Fascial/Stick-For-Blind/photos/image2.jpg

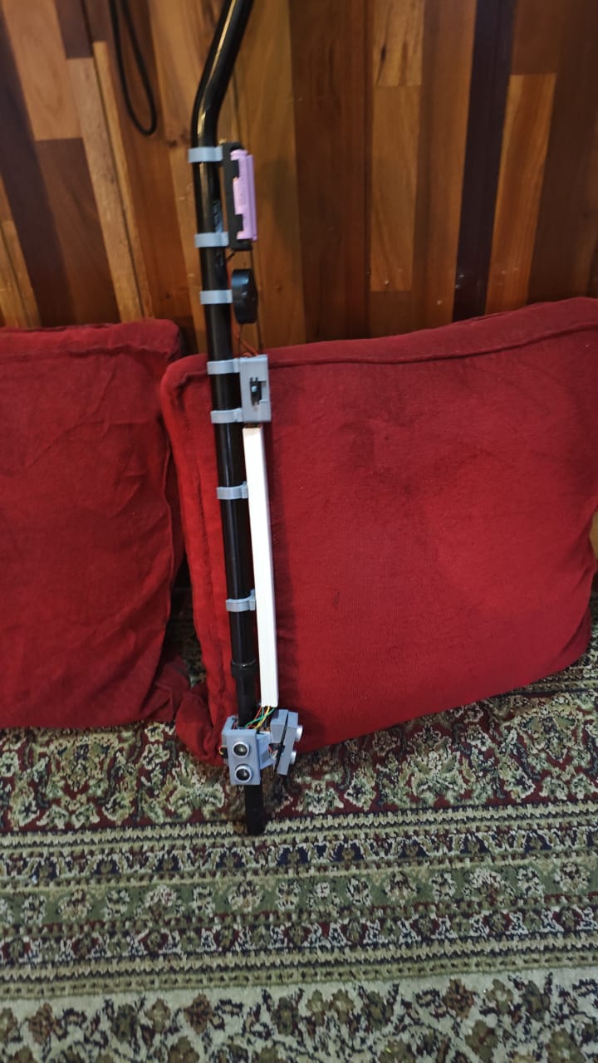
photos/image2.jpg
